DigitalWorkz/eZ_Navi-Delete/img/pwa/baseConfigurationPWA.png

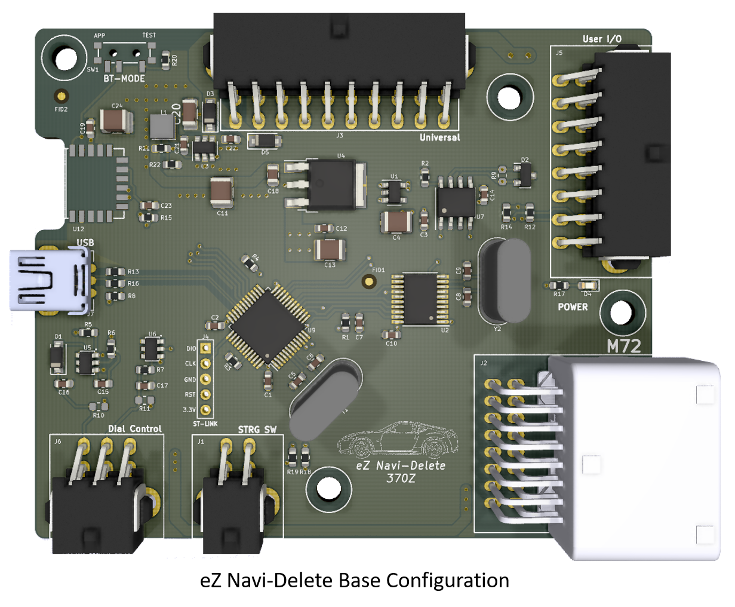
img/pwa/baseConfigurationPWA.png
