DigitalWorkz/eZ_Navi-Delete/img/pwa/bluetoothAddon.png

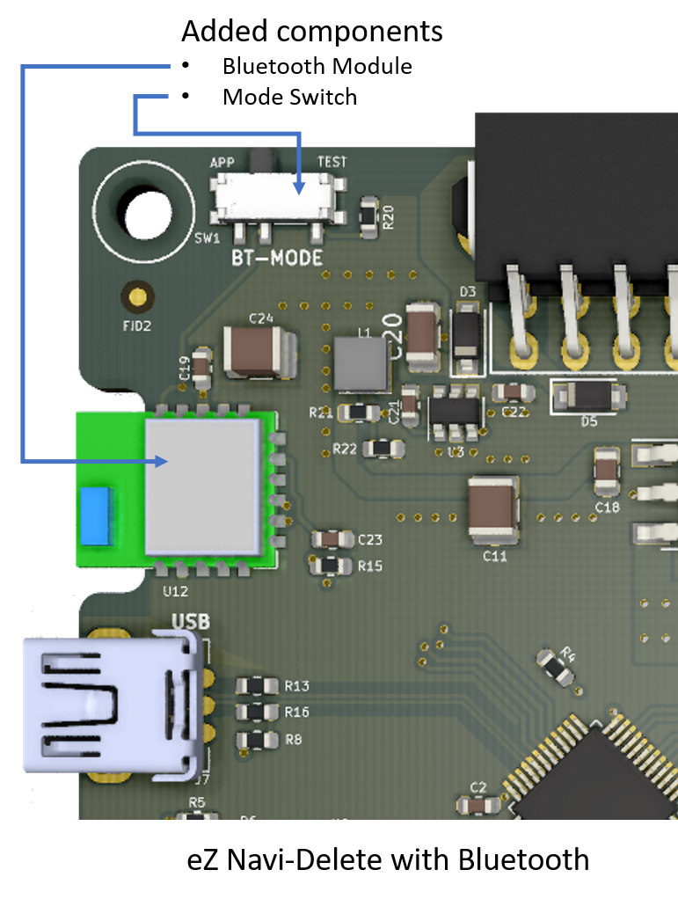
img/pwa/bluetoothAddon.png
