DigitalWorkz/eZ_Navi-Delete/img/pwa/hw1p0a_silk_error.png

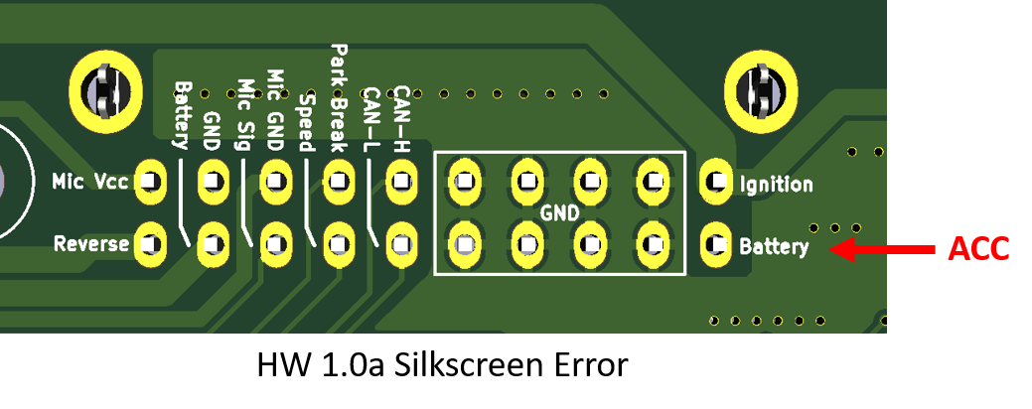
img/pwa/hw1p0a_silk_error.png
