DigitalWorkz/eZ_Navi-Delete/img/pwa/hw1p0b_PWA.png

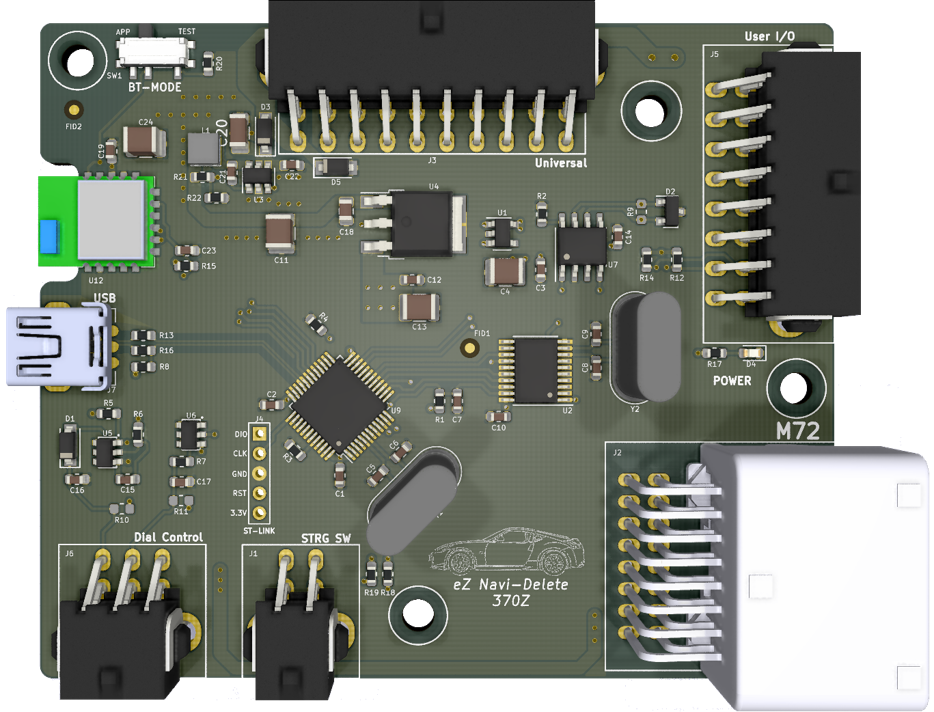
img/pwa/hw1p0b_PWA.png
