DigitalWorkz/eZ_Navi-Delete/img/pwa/hw2p0a_PWA.png

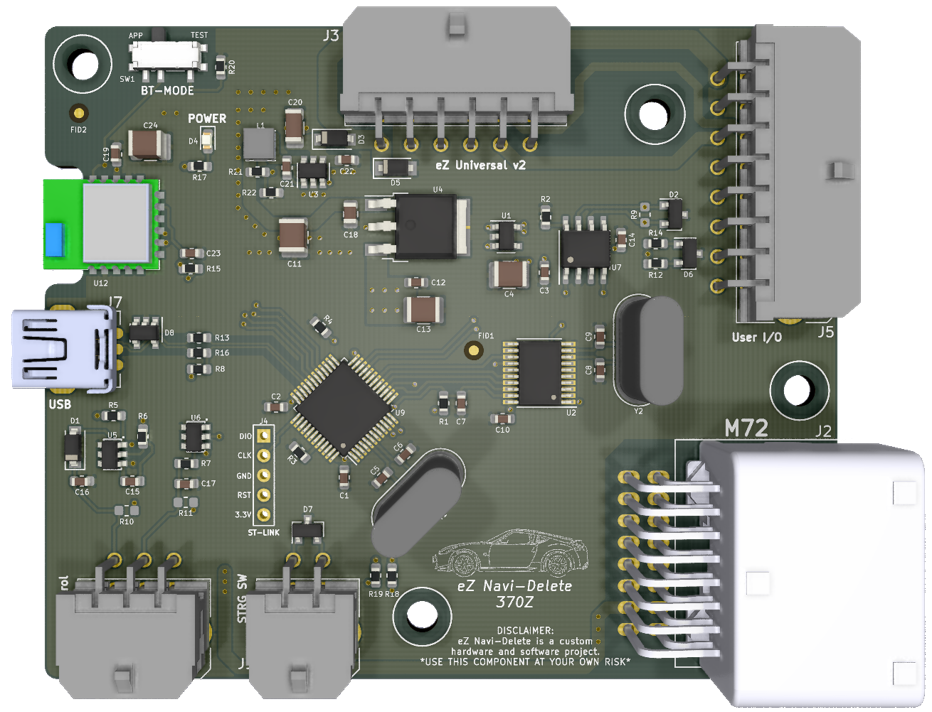
img/pwa/hw2p0a_PWA.png
