DigitalWorkz/eZ_Navi-Delete/img/support/370ZClimateControlSwitch.jpg

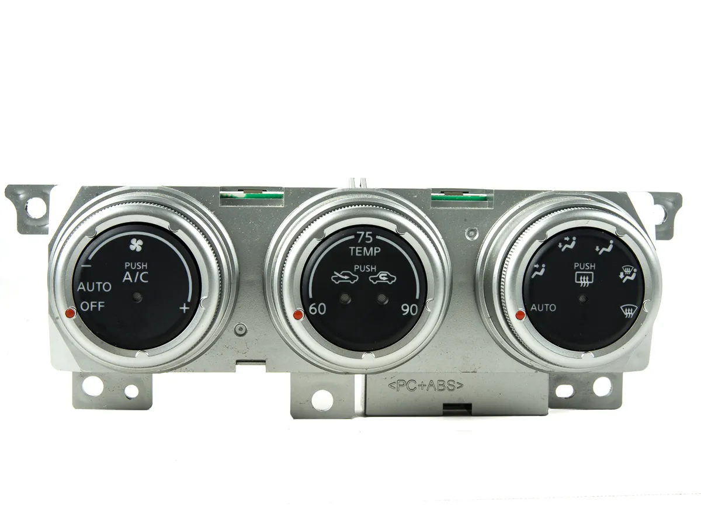
img/support/370ZClimateControlSwitch.jpg
