DigitalWorkz/eZ_Navi-Delete/img/support/370ZClimateControlSwitch_back.png

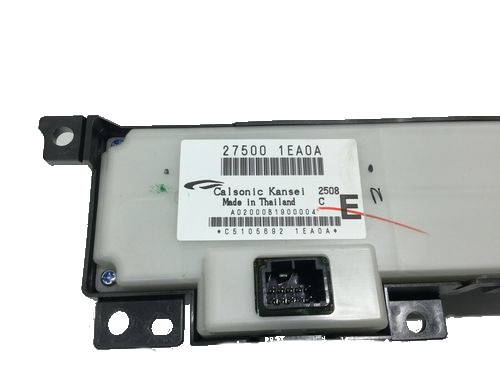
img/support/370ZClimateControlSwitch_back.png
