DigitalWorkz/eZ_Navi-Delete/img/support/eZNaviDelete_0p7.png

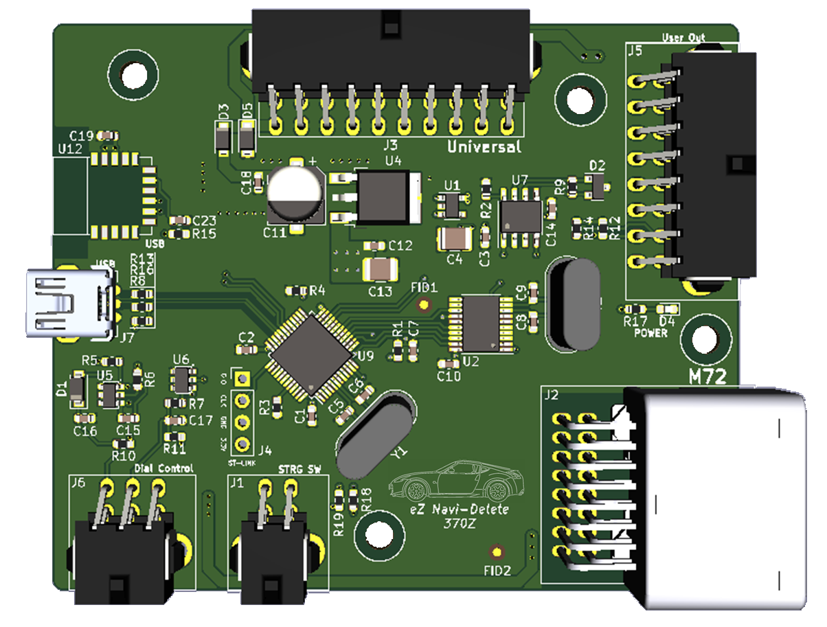
img/support/eZNaviDelete_0p7.png
