DigitalWorkz/eZ_Navi-Delete/img/support/v1p0a_silkscreenError.jpg

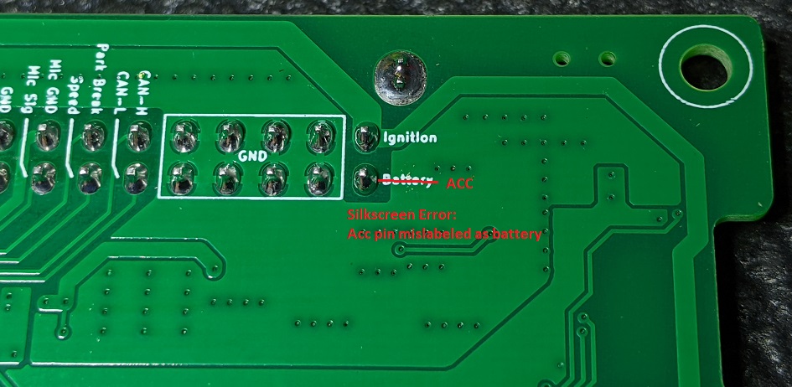
img/support/v1p0a_silkscreenError.jpg
