DigitalWorkz/eZ_Navi-Delete/img/wiring/2p0a/base_model_ac_control_module_harness_pinout.png

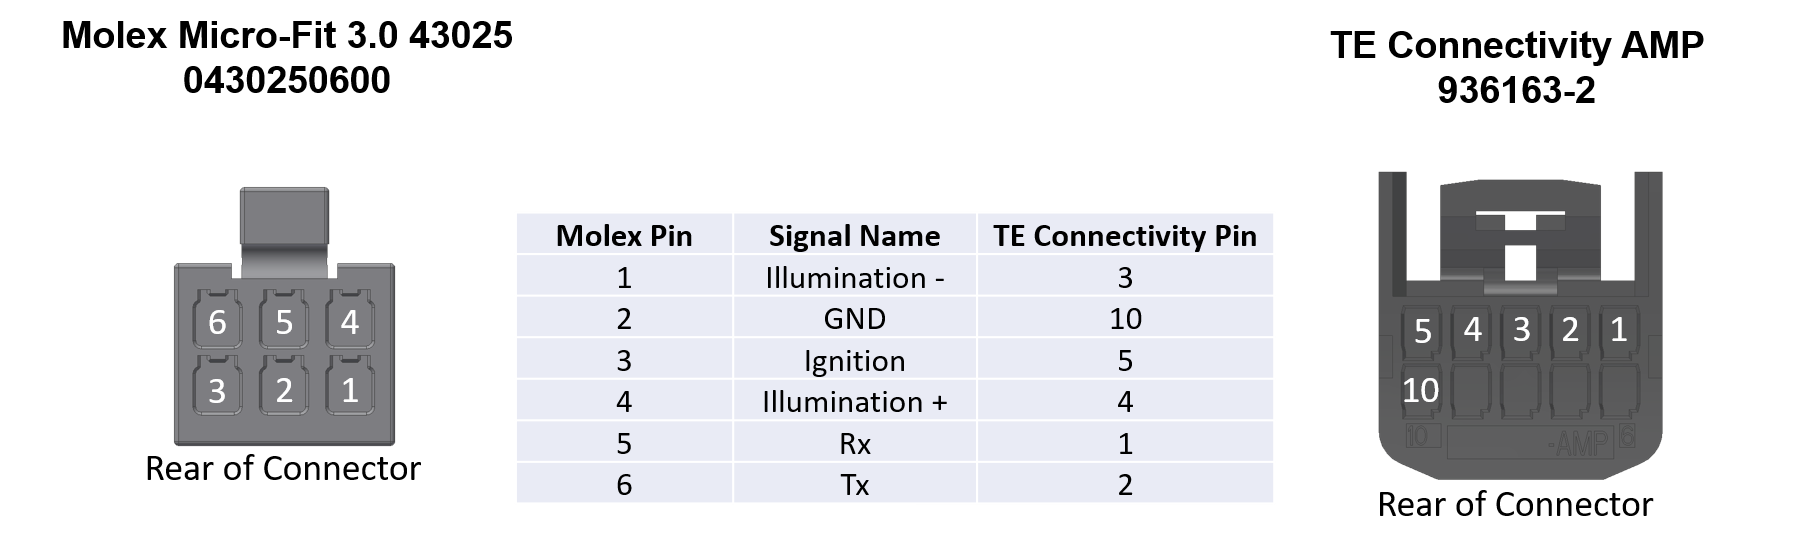
img/wiring/2p0a/base_model_ac_control_module_harness_pinout.png
