DigitalWorkz/eZ_Navi-Delete/img/wiring/2p0a/ezNaviDelete_steeringWheelConnectorJ1_pinout.png

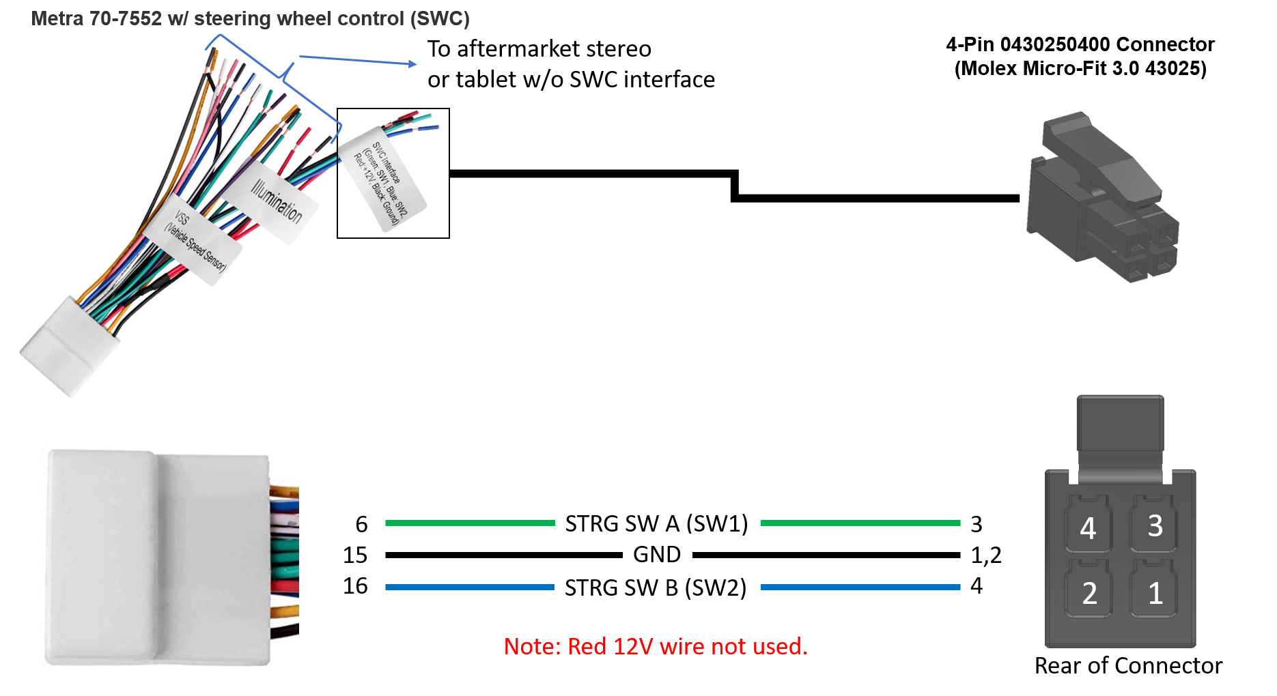
img/wiring/2p0a/ezNaviDelete_steeringWheelConnectorJ1_pinout.png
