DigitalWorkz/eZ_Navi-Delete/img/wiring/2p0a/FactoryHarnessAdapter_12-pin_pinout.png

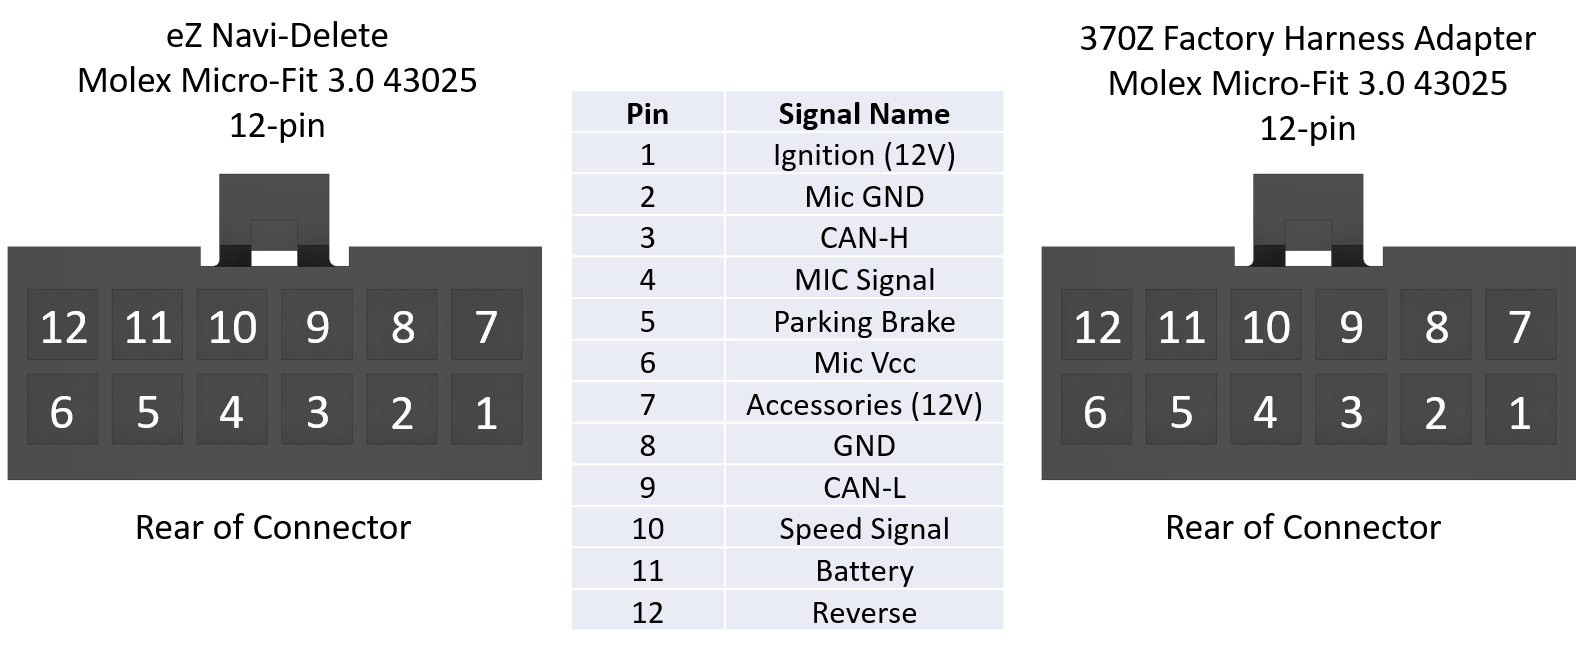
img/wiring/2p0a/FactoryHarnessAdapter_12-pin_pinout.png
