DigitalWorkz/eZ_Navi-Delete/img/wiring/32pin_universalAdapter_pinout.png

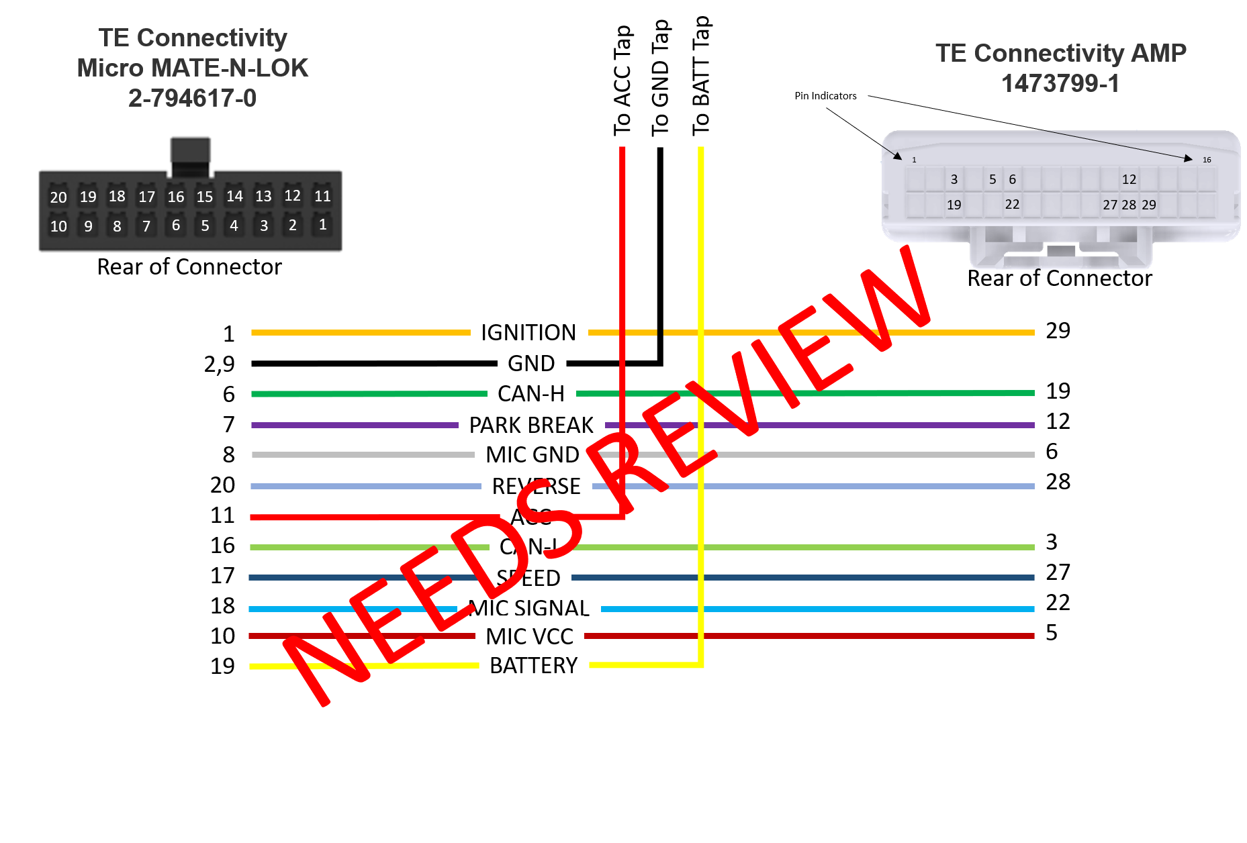
img/wiring/32pin_universalAdapter_pinout.png
