DigitalWorkz/eZ_Navi-Delete/img/support/bringup/ez_build_complete.png

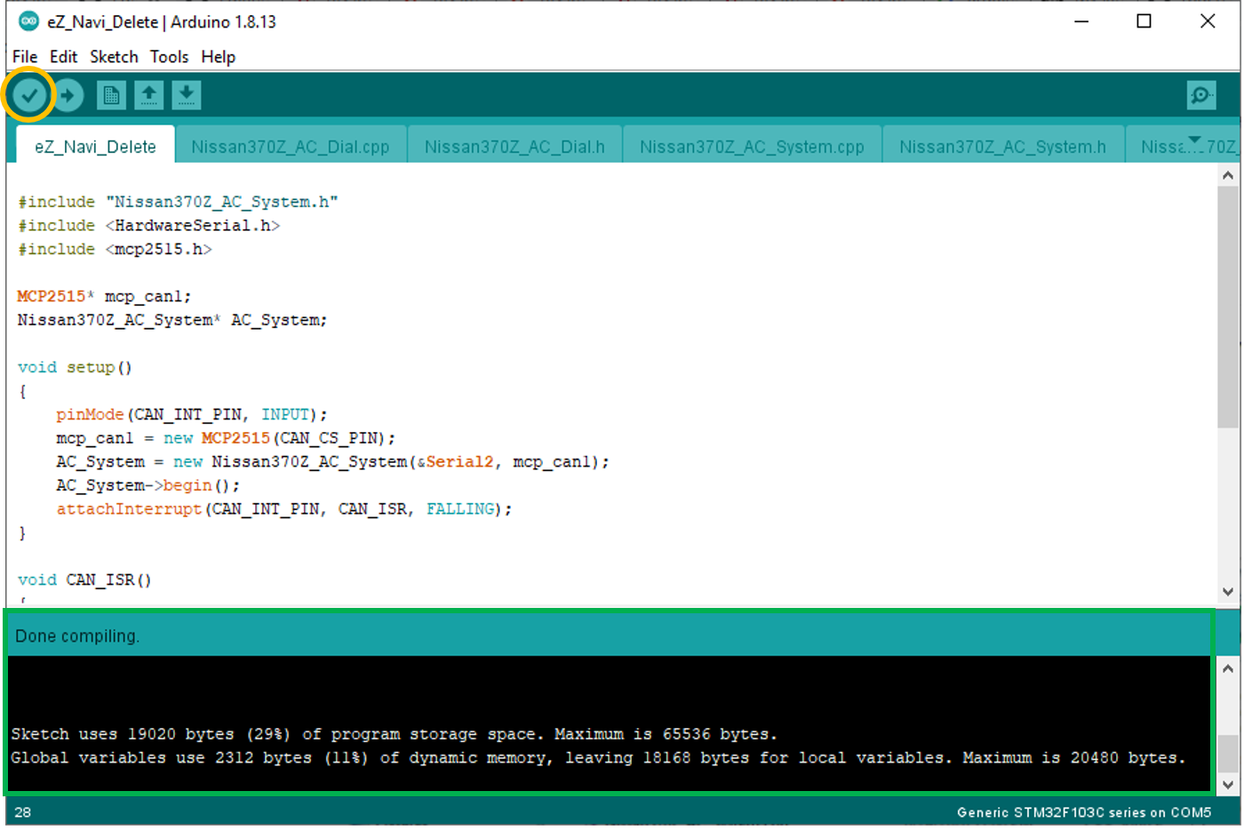
img/support/bringup/ez_build_complete.png
