DigitalWorkz/eZ_Navi-Delete/img/support/bringup/install_lib.png

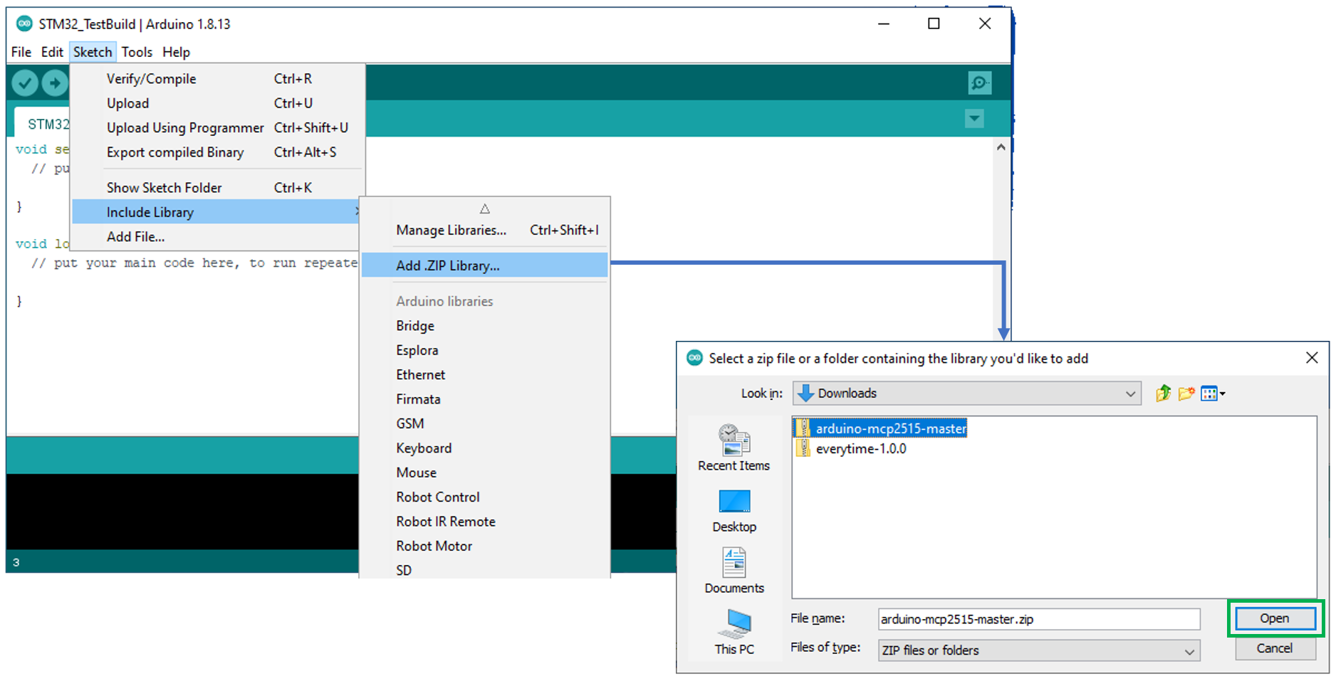
img/support/bringup/install_lib.png
