DigitalWorkz/eZ_Navi-Delete/img/support/bringup/install_STM32_core.png

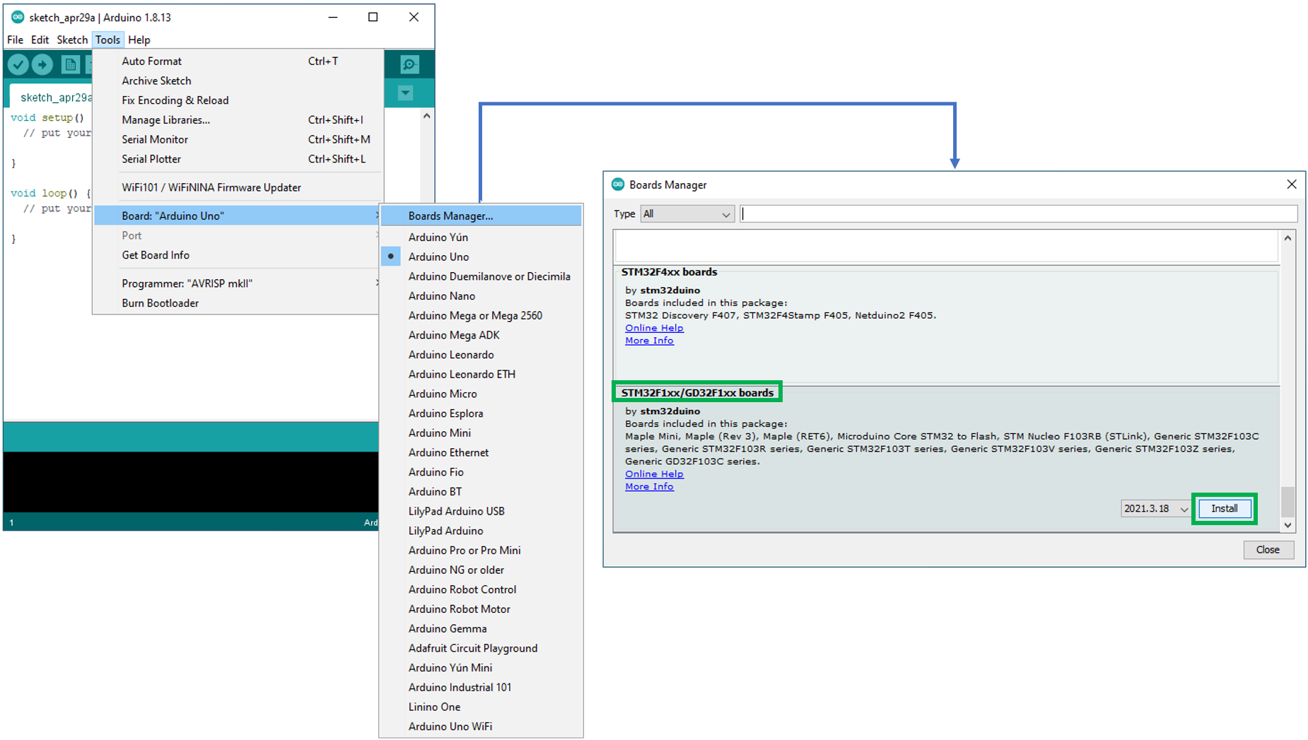
img/support/bringup/install_STM32_core.png
