DigitalWorkz/eZ_Navi-Delete/img/support/bringup/installing_drivers.png

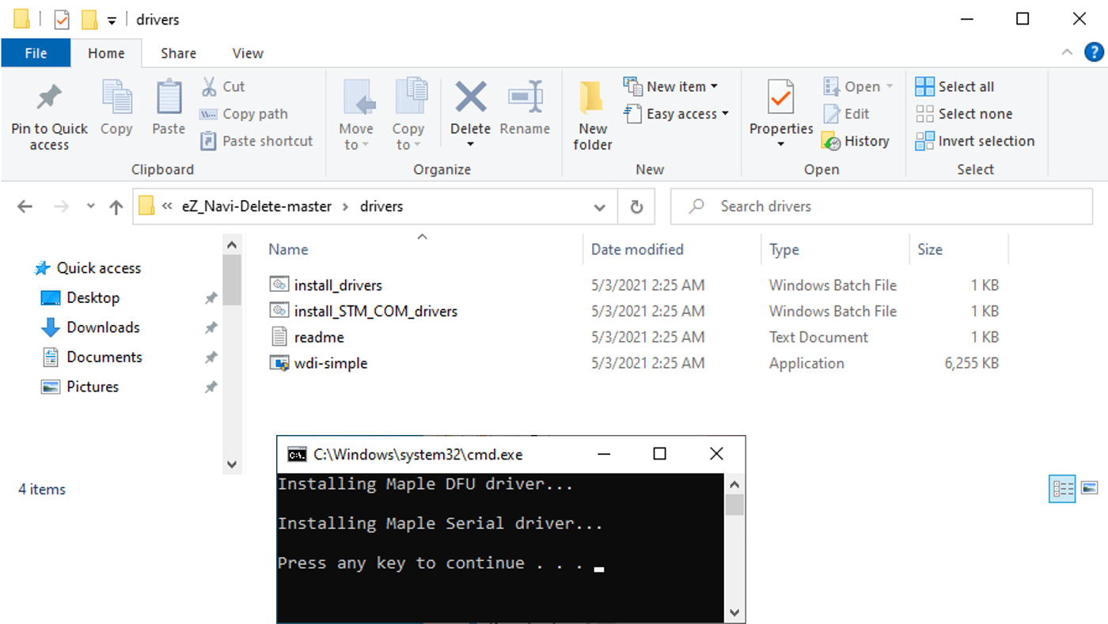
img/support/bringup/installing_drivers.png
