DigitalWorkz/eZ_Navi-Delete/img/wiring/2p0a/2009_harnessAdapterDiagram.png

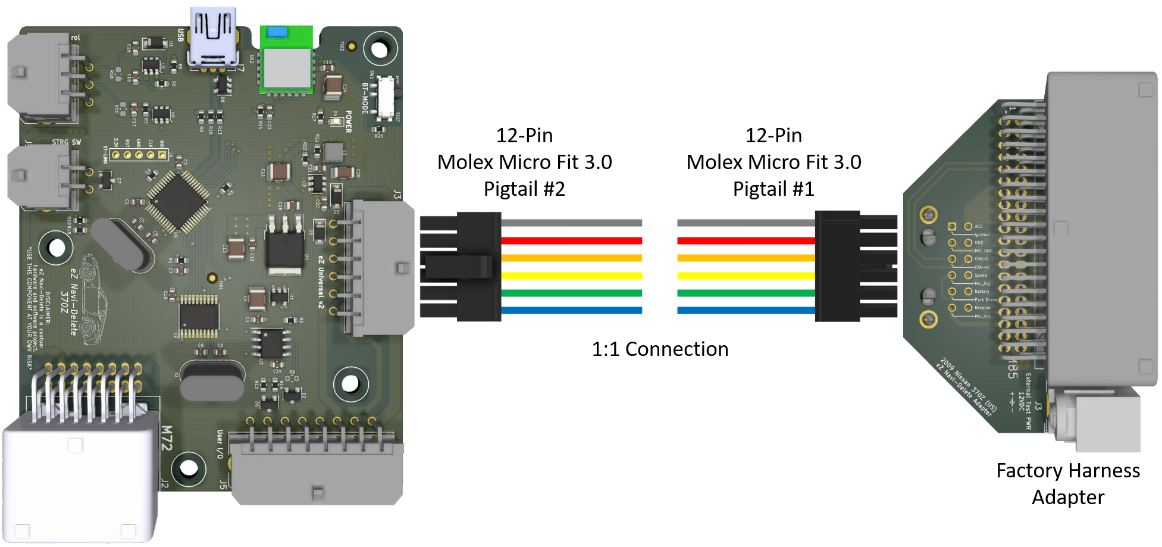
img/wiring/2p0a/2009_harnessAdapterDiagram.png
