DigitalWorkz/eZ_Navi-Delete/img/wiring/2p0a/2010_universalWiringHarnessAdapterPinout.png

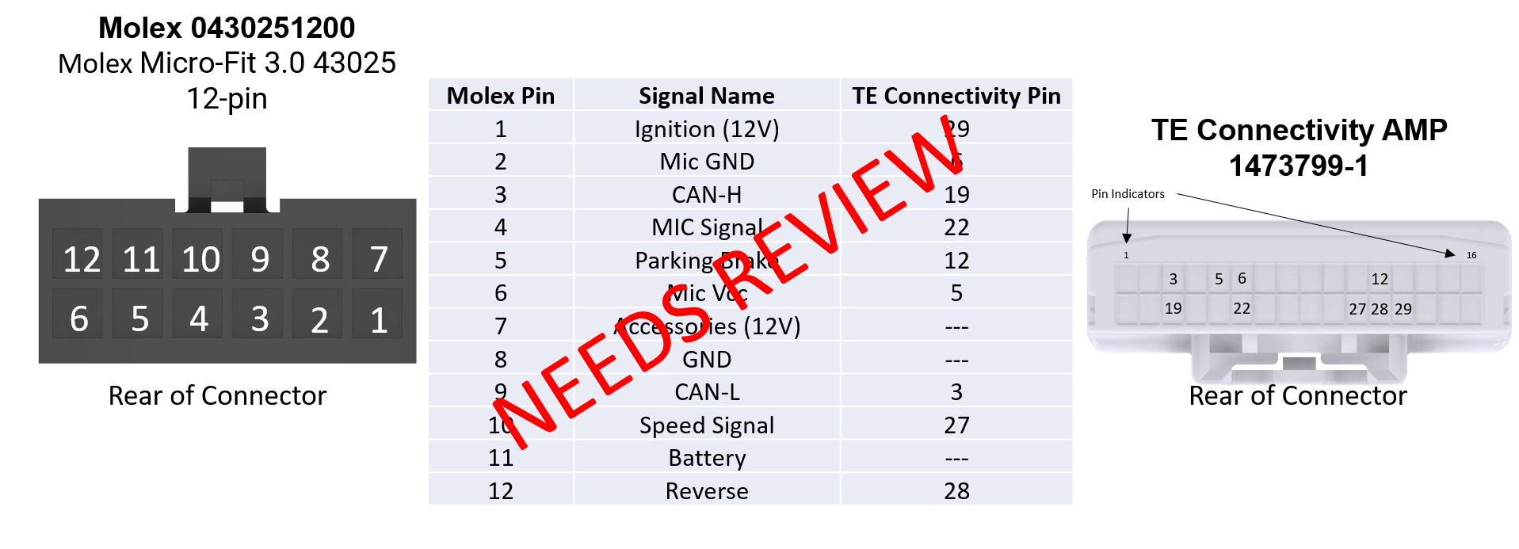
img/wiring/2p0a/2010_universalWiringHarnessAdapterPinout.png
