DigitalWorkz/eZ_Navi-Delete/img/wiring/2p0a/eZNaviDelete_UserOutConnectorJ5.png

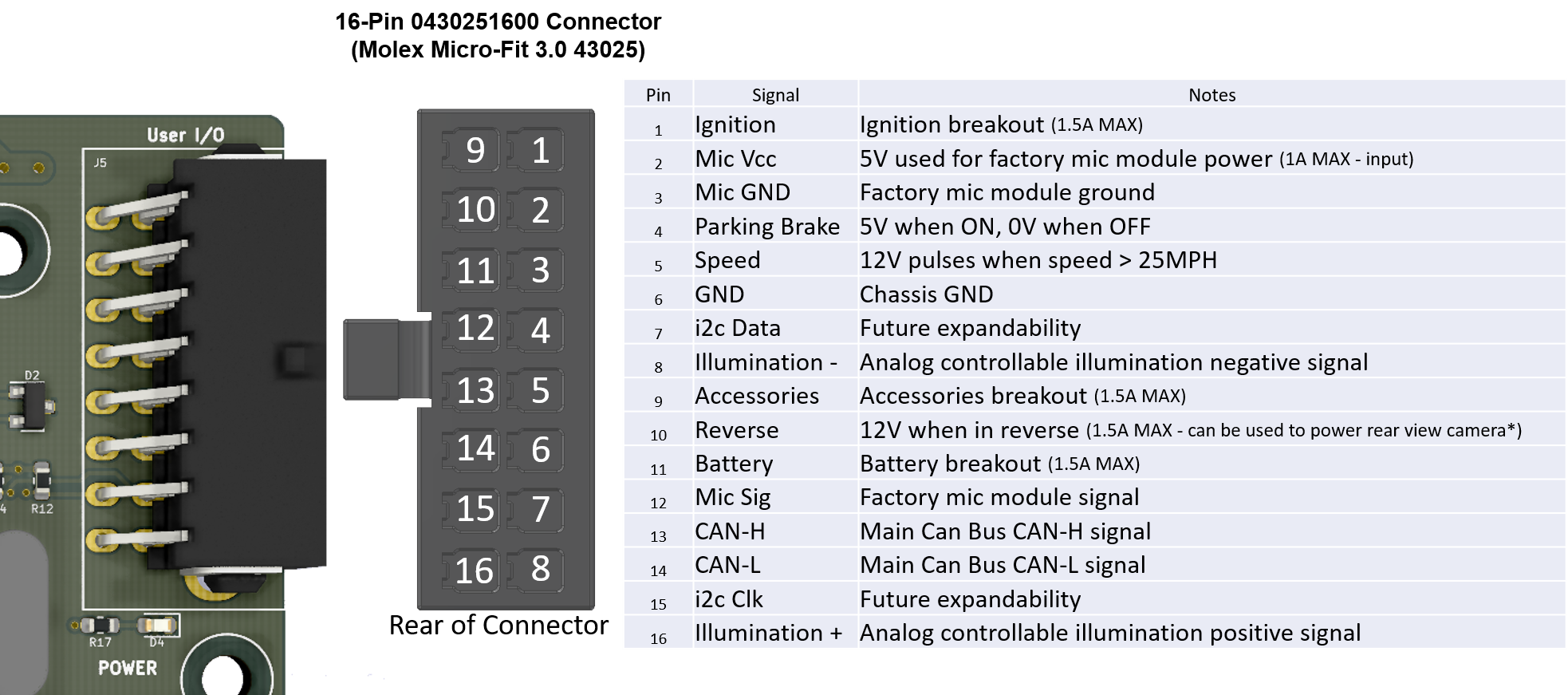
img/wiring/2p0a/eZNaviDelete_UserOutConnectorJ5.png
