DigitalWorkz/eZ_Navi-Delete/img/wiring/370ZClimateControlSwitch.png

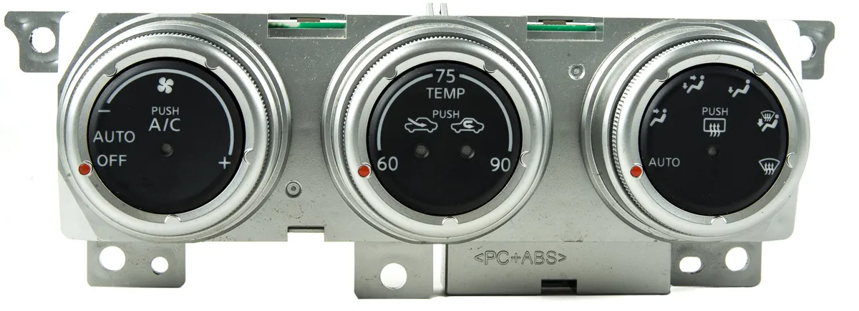
img/wiring/370ZClimateControlSwitch.png
