DigitalWorkz/eZ_Navi-Delete/img/wiring/ACdialControlModuleConnectorJ6.png

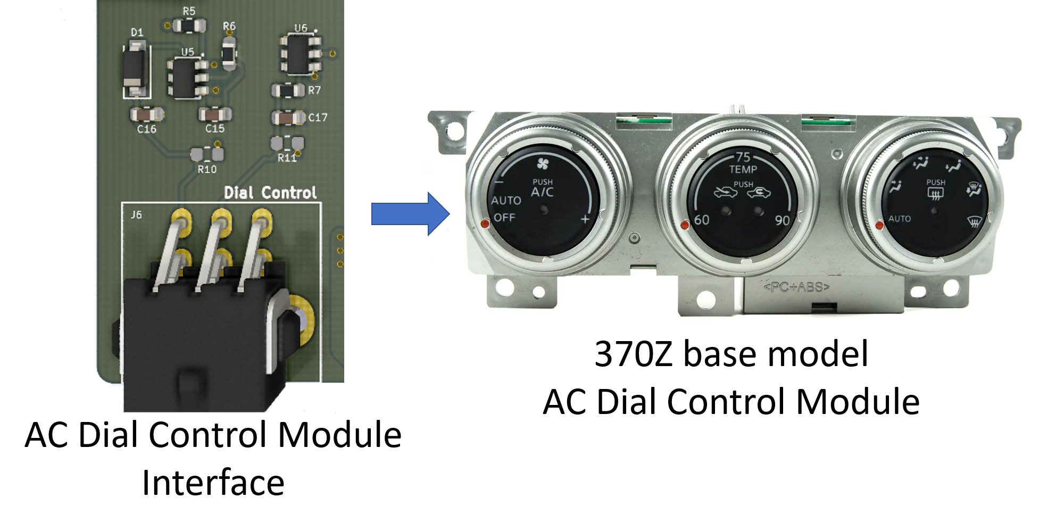
img/wiring/ACdialControlModuleConnectorJ6.png
