DigitalWorkz/eZ_Navi-Delete/img/wiring/base_model_ac_control_module_to_eZNaviDelete.png

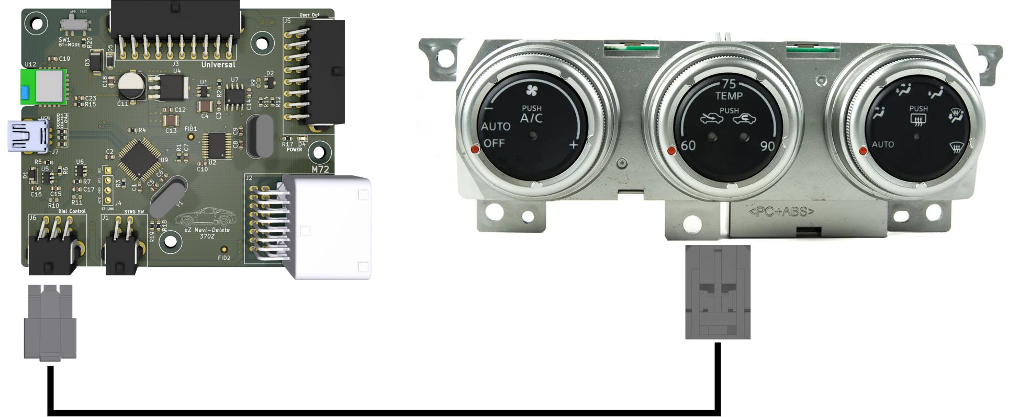
img/wiring/base_model_ac_control_module_to_eZNaviDelete.png
