DigitalWorkz/eZ_Navi-Delete/img/wiring/eZNaviDelete_UniversalConnectorJ3.png

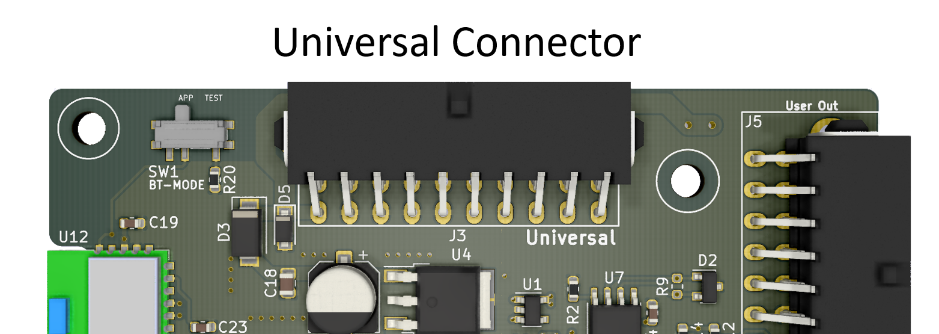
img/wiring/eZNaviDelete_UniversalConnectorJ3.png
