DigitalWorkz/eZ_Navi-Delete/img/wiring/SWC_to_eZNaviDelete.png

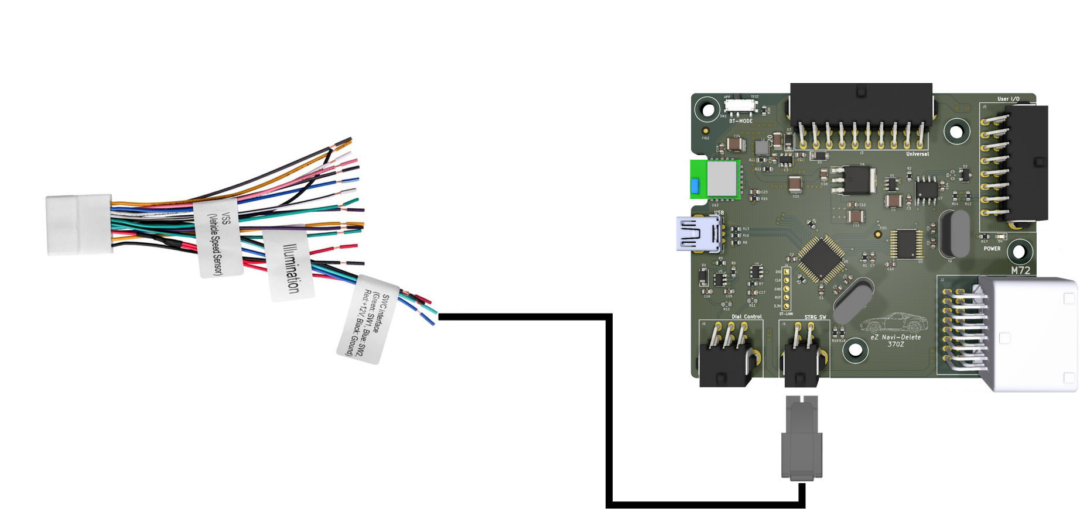
img/wiring/SWC_to_eZNaviDelete.png
