DigitalWorkz/eZ_Navi-Delete/img/support/bringup/adding_STM32_core_url.png

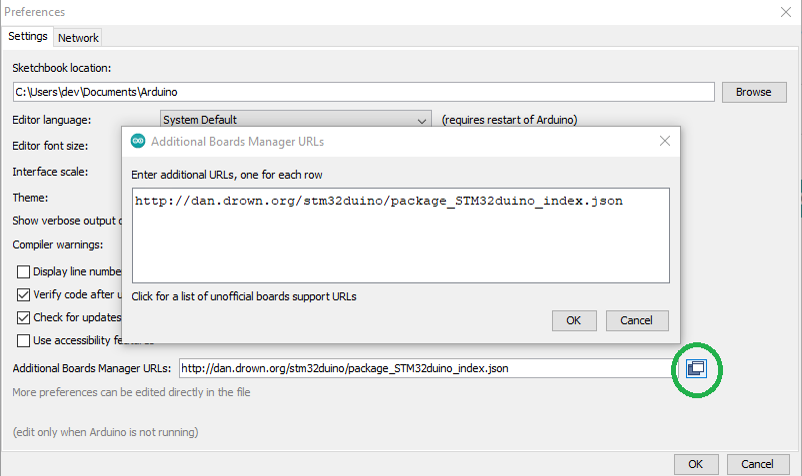
img/support/bringup/adding_STM32_core_url.png
