DigitalWorkz/eZ_Navi-Delete/img/support/bringup/com_select_maple.png

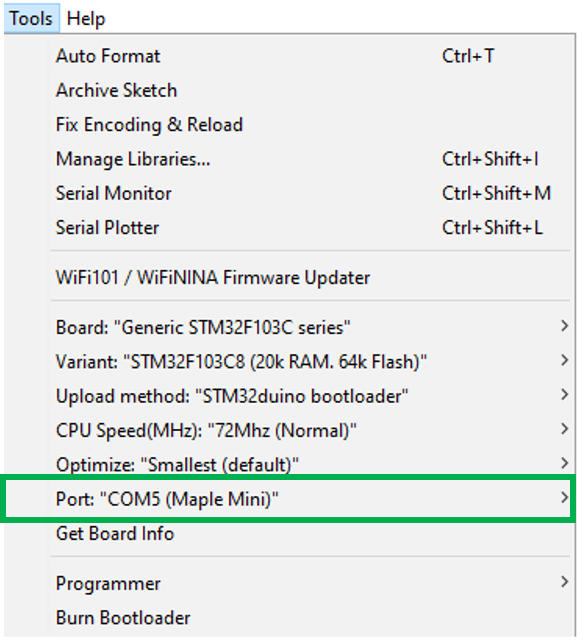
img/support/bringup/com_select_maple.png
