DigitalWorkz/eZ_Navi-Delete/img/support/bringup/confirm_STM32_avail.png

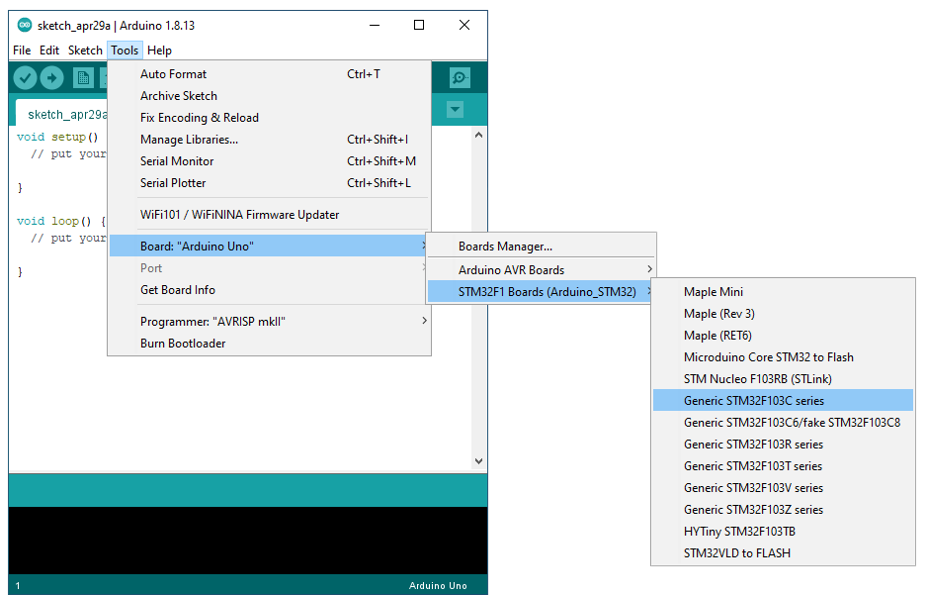
img/support/bringup/confirm_STM32_avail.png
