DigitalWorkz/eZ_Navi-Delete/img/support/bringup/dl_drivers.png

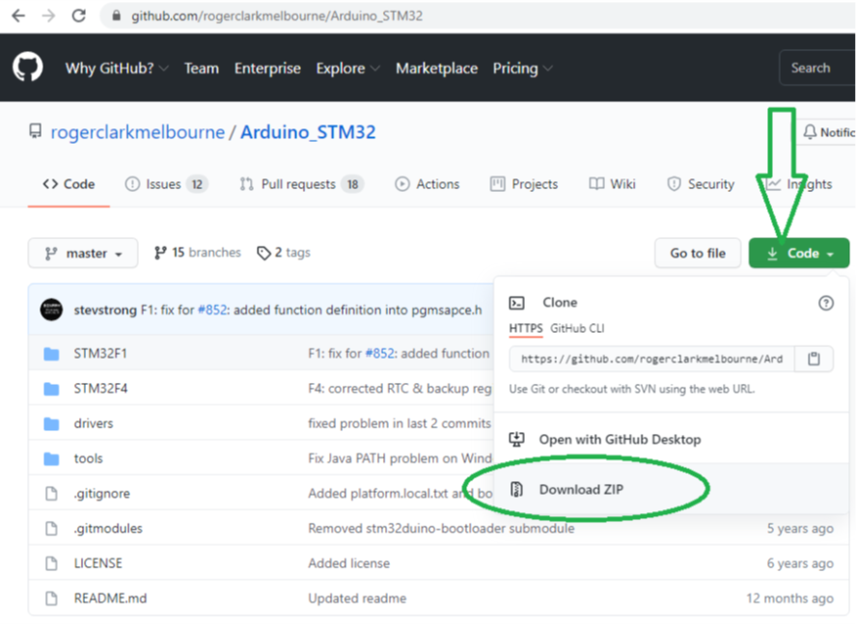
img/support/bringup/dl_drivers.png
