DigitalWorkz/eZ_Navi-Delete/img/support/bringup/ez_flash_complete.png

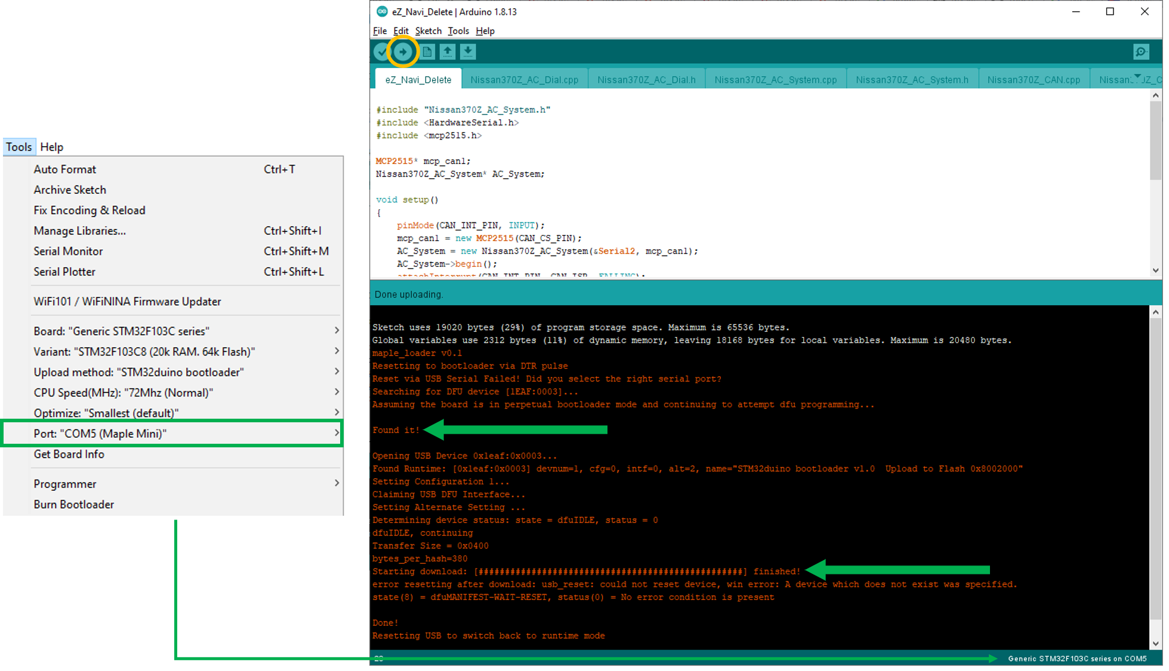
img/support/bringup/ez_flash_complete.png
