DigitalWorkz/eZ_Navi-Delete/img/support/bringup/launch_ino.png

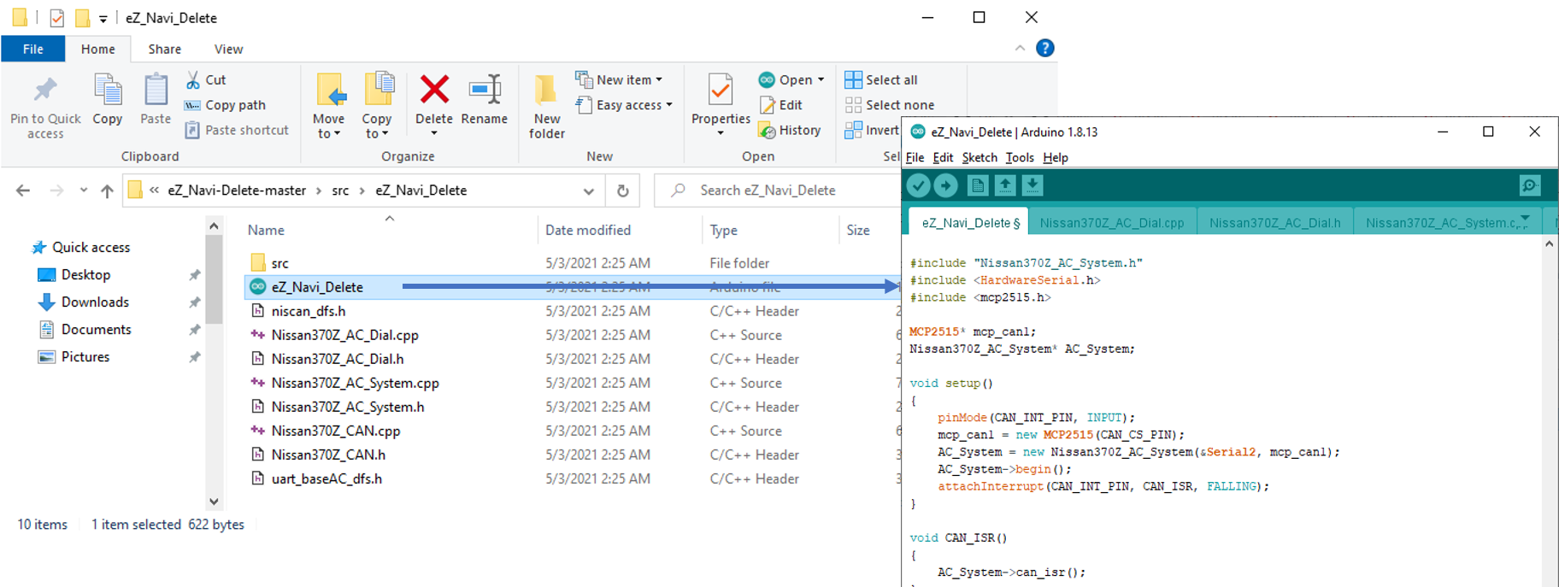
img/support/bringup/launch_ino.png
