DigitalWorkz/eZ_Navi-Delete/img/support/bringup/power_stlink.png

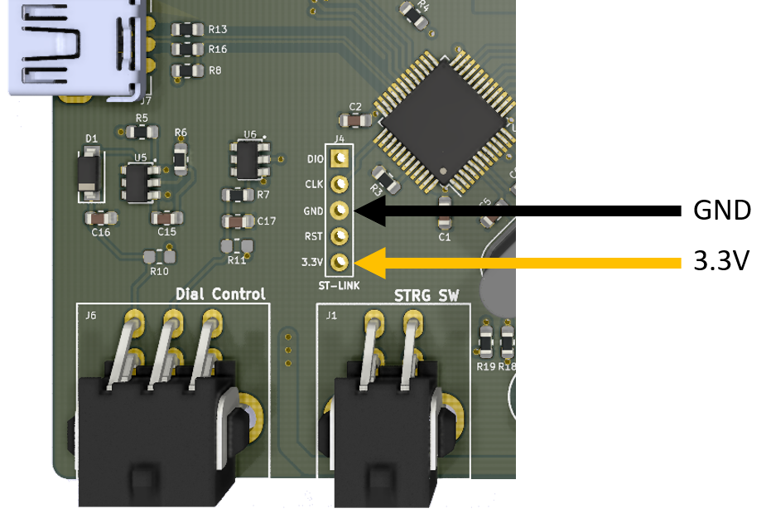
img/support/bringup/power_stlink.png
