DigitalWorkz/eZ_Navi-Delete/img/support/bringup/power_universal.png

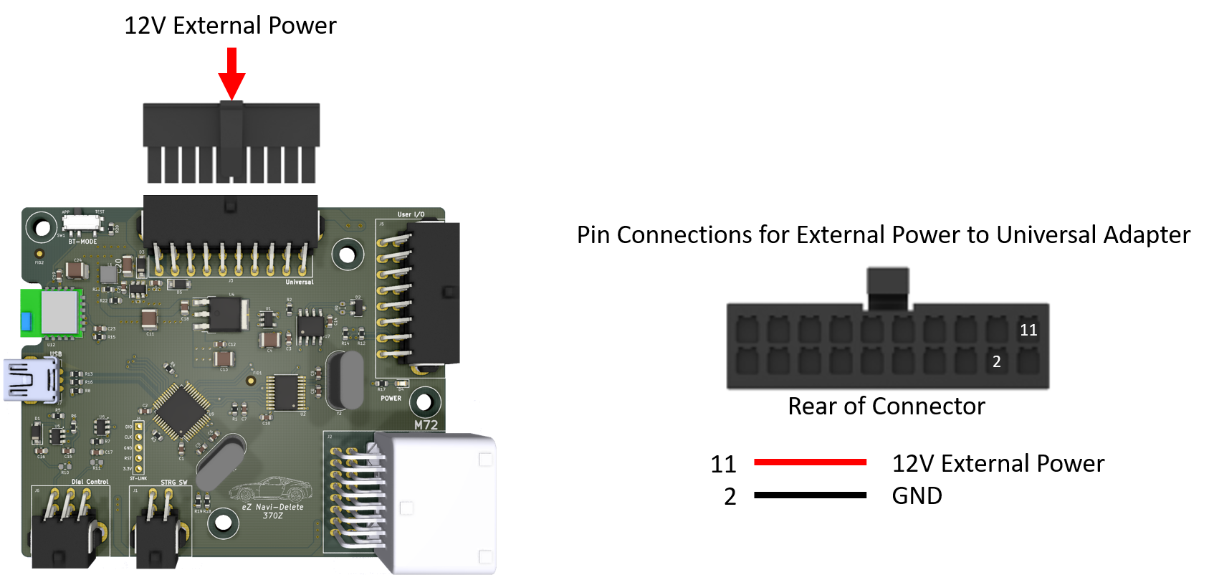
img/support/bringup/power_universal.png
