DigitalWorkz/eZ_Navi-Delete/img/support/bringup/power_user.png

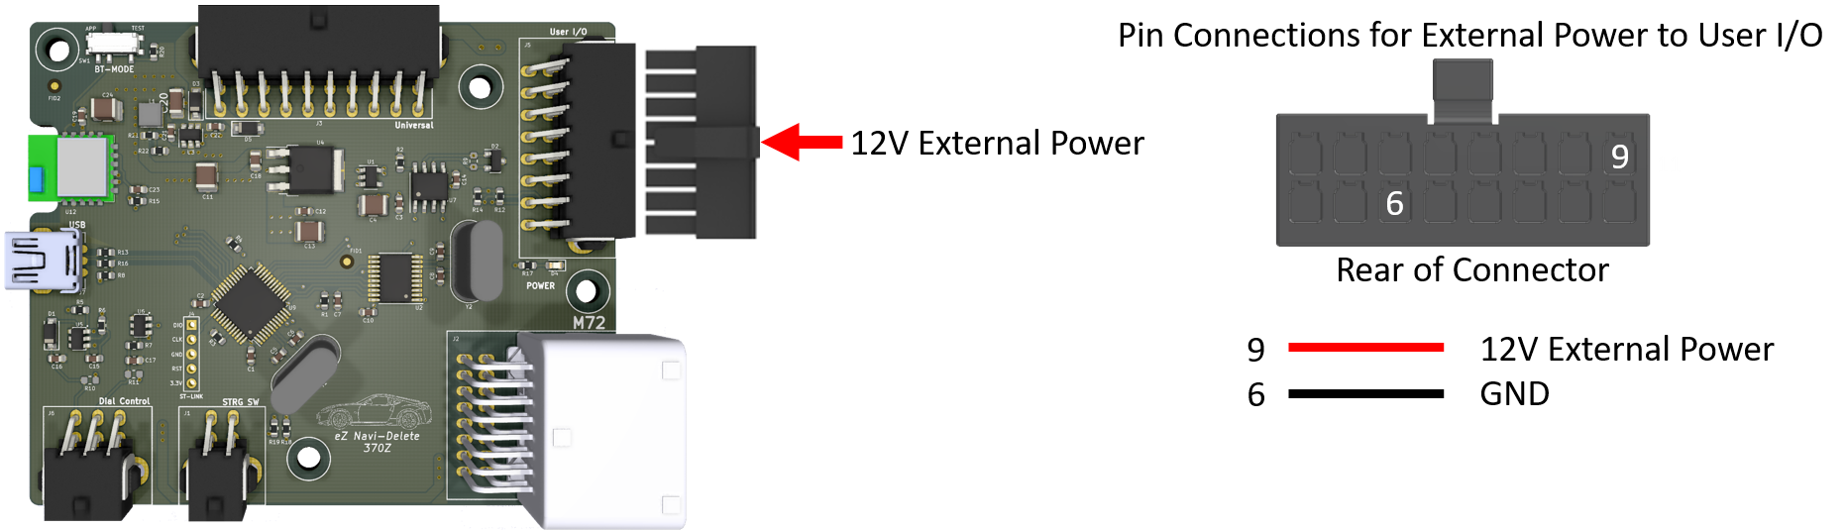
img/support/bringup/power_user.png
