DigitalWorkz/eZ_Navi-Delete/img/support/bringup/set_settings_test.png

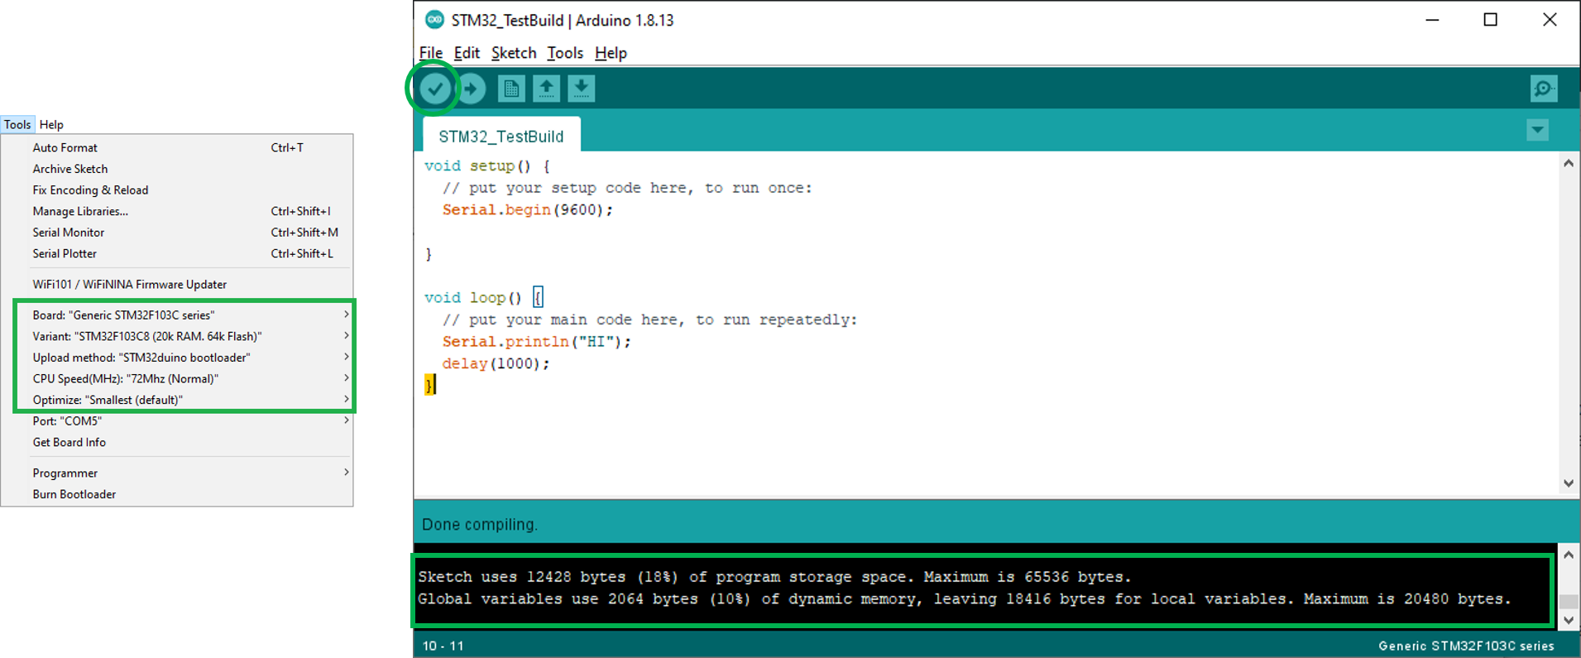
img/support/bringup/set_settings_test.png
